aeonSolutions/AeonLabs-WIFI-BLE-RFID-NFC-Desk-Contacless-Reader-Writer/designs/pcb.fw.png

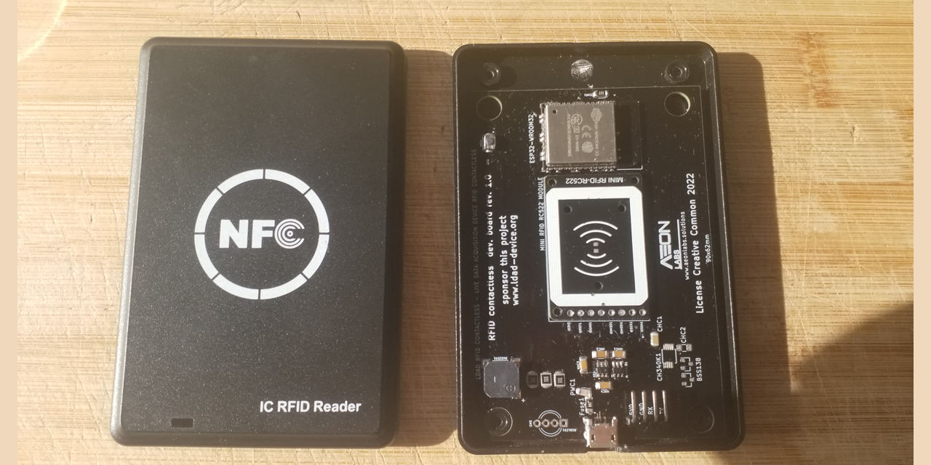
designs/pcb.fw.png
